RomanAlexandroff/42-Prague-Smart-Sign/docs/3d_model/42_sign_frame_dimensions.png

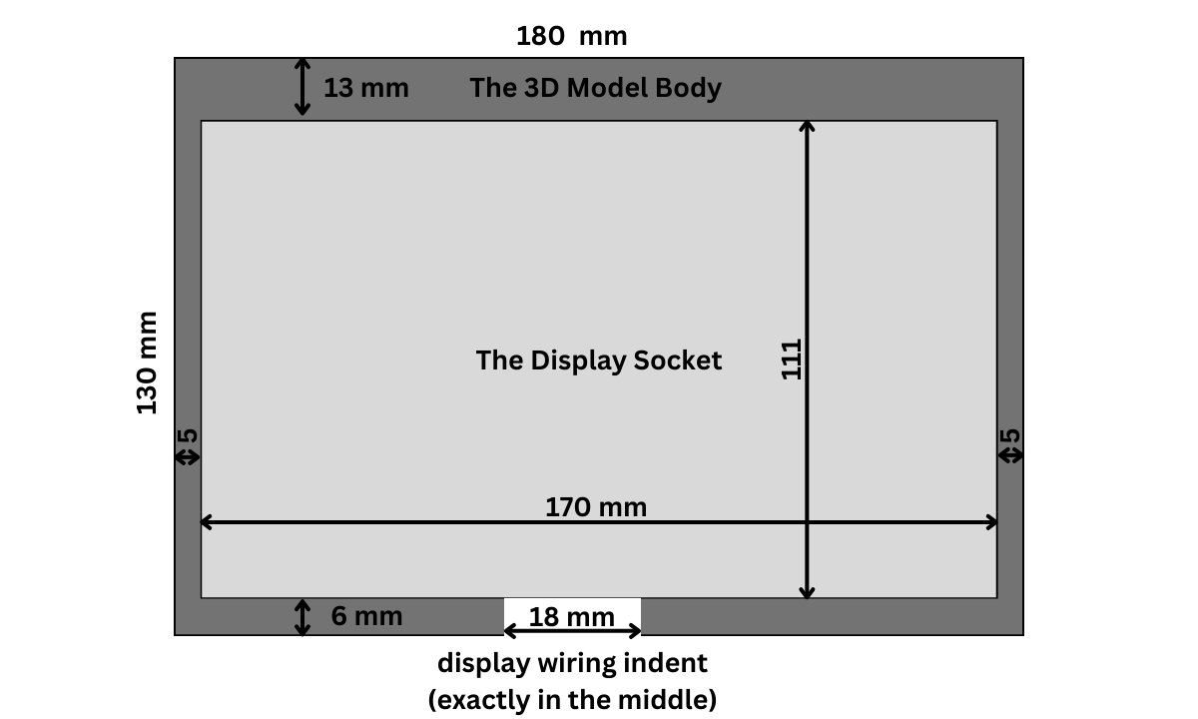
docs/3d_model/42_sign_frame_dimensions.png
