RomanAlexandroff/42-Prague-Smart-Sign/docs/graphic_materials/intra_error_img.bmp

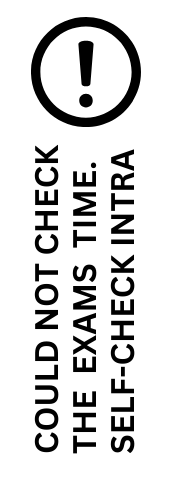
docs/graphic_materials/intra_error_img.bmp
