RomanAlexandroff/42-Prague-Smart-Sign/docs/graphic_materials/preexam_5mins_img.bmp

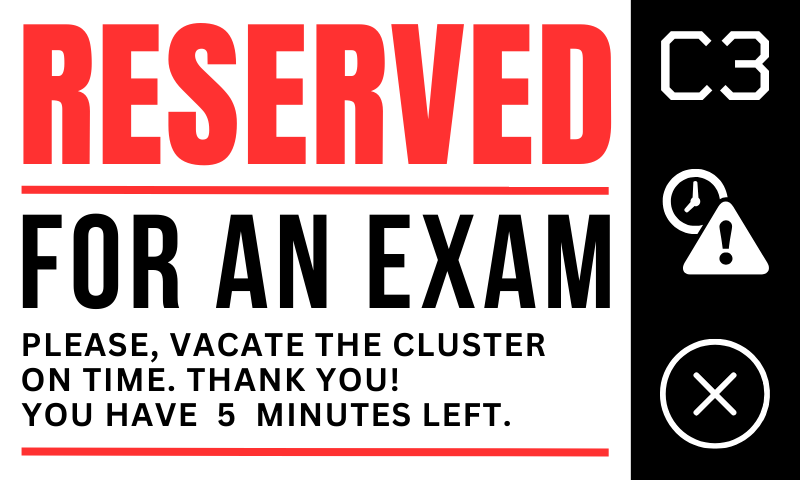
docs/graphic_materials/preexam_5mins_img.bmp
