RomanAlexandroff/42-Prague-Smart-Sign/docs/finished_device/42_Cluster_Sign_result0.jpeg

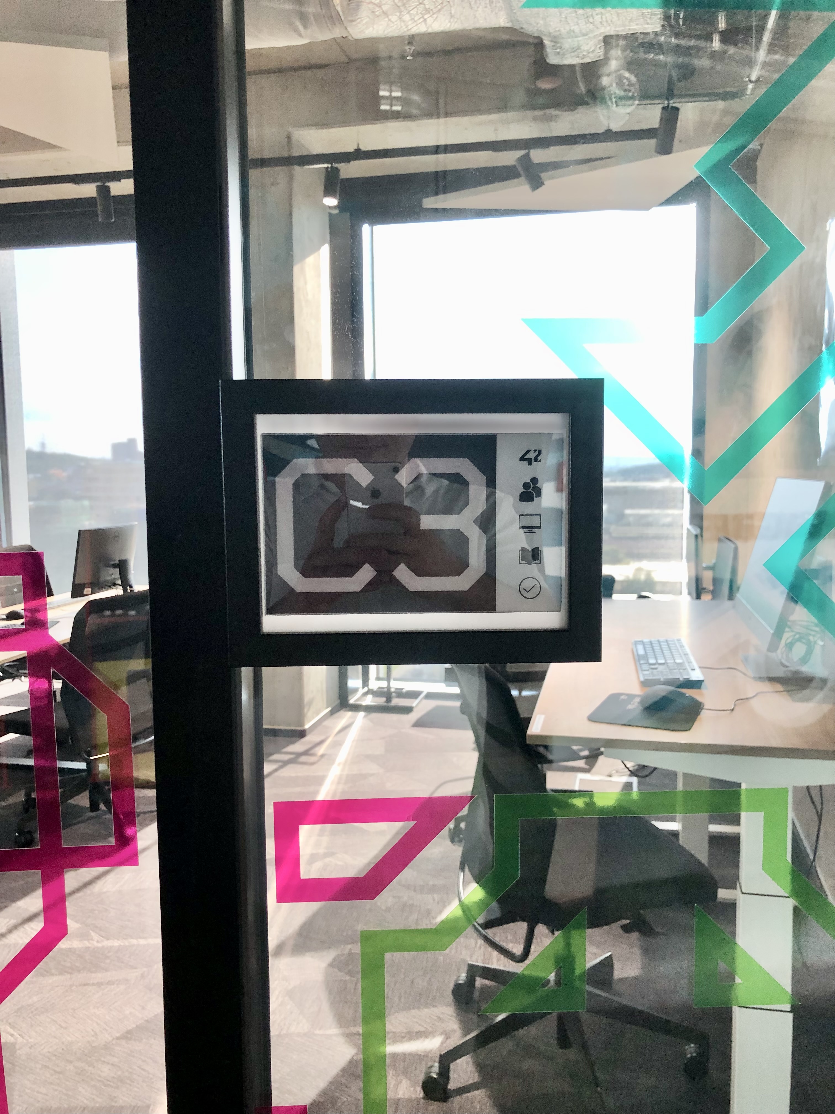
docs/finished_device/42_Cluster_Sign_result0.jpeg
