RomanAlexandroff/42-Prague-Smart-Sign/docs/finished_device/42_Cluster_Sign_result2.jpeg

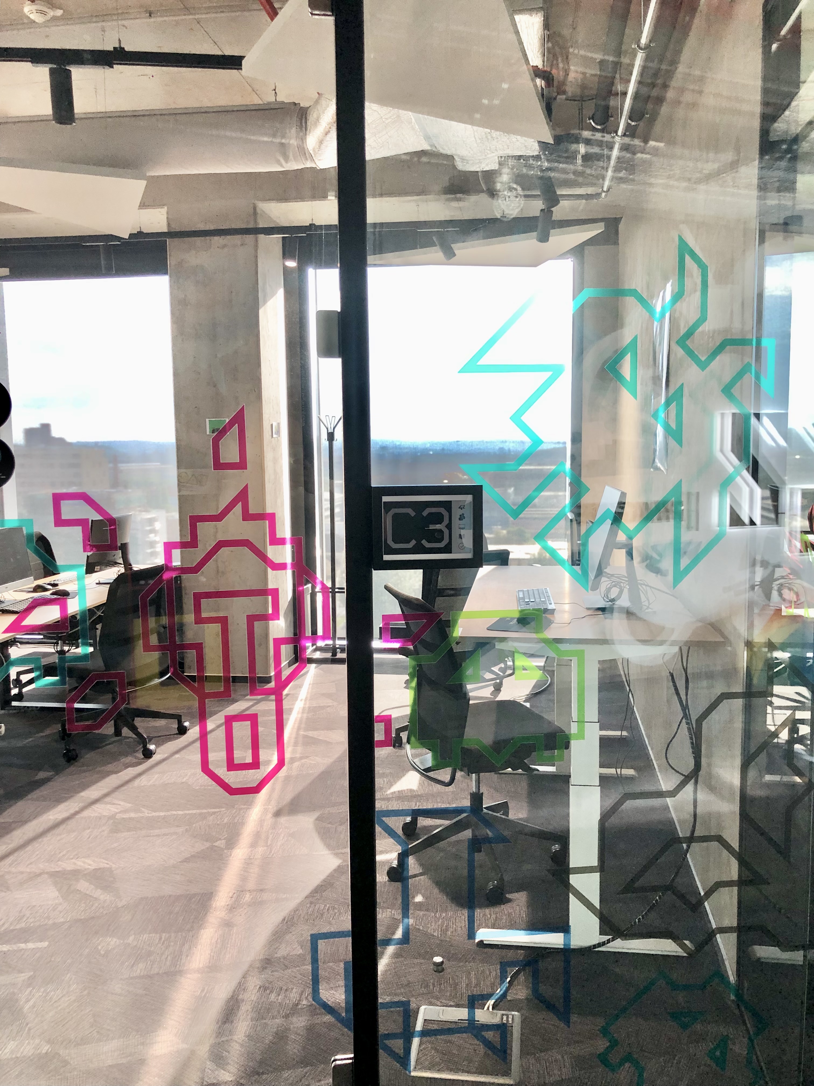
docs/finished_device/42_Cluster_Sign_result2.jpeg
